WilliTourt/STM32-Desktop-Drumkit/Hardware/Schematic & PCB/Images/MotherBoard_PCB_Bottom.png

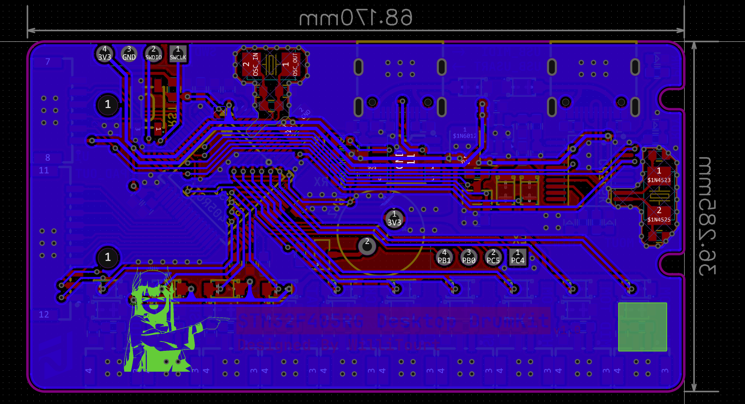
Hardware/Schematic & PCB/Images/MotherBoard_PCB_Bottom.png
