WilliTourt/STM32-Desktop-Drumkit/Hardware/Schematic & PCB/Images/UI_PCB_Top.png

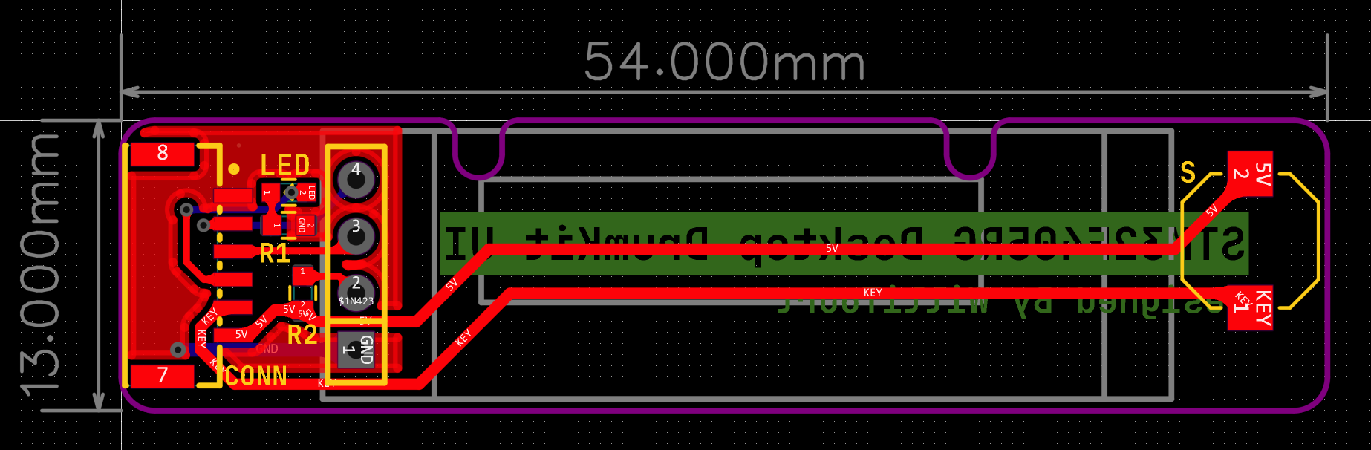
Hardware/Schematic & PCB/Images/UI_PCB_Top.png
