WilliTourt/STM32-Desktop-Drumkit/Images/IMG_20251013_194556.jpg

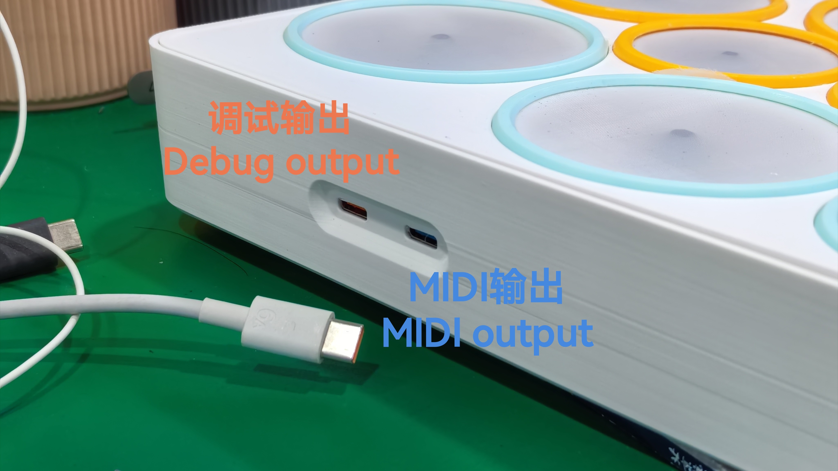
Images/IMG_20251013_194556.jpg
