WilliTourt/STM32-Desktop-Drumkit/Images/IMG_20251013_195028.jpg

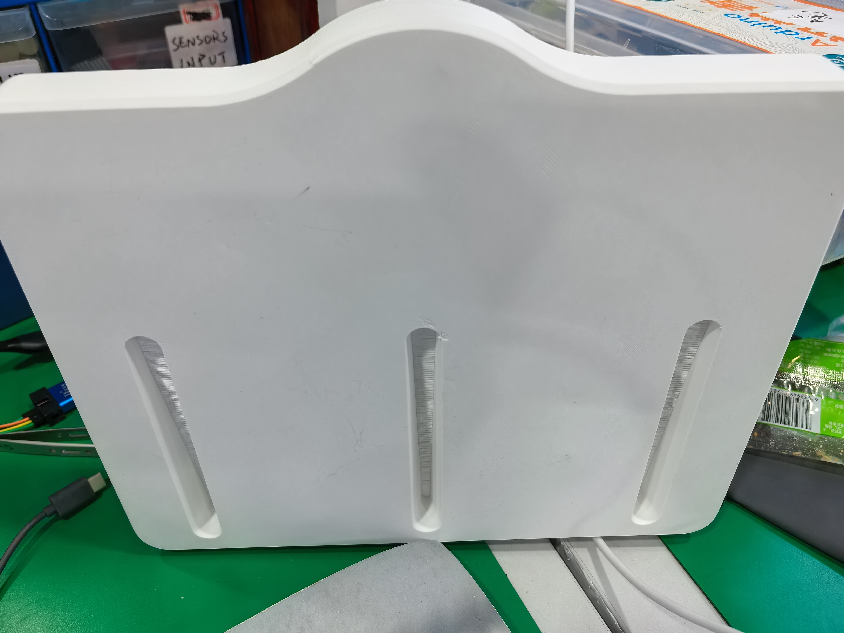
Images/IMG_20251013_195028.jpg
