WilliTourt/STM32-Desktop-Drumkit/Hardware/3D Files/SolidWorks/Tests/DrumpadTestAssemble.SLDASM

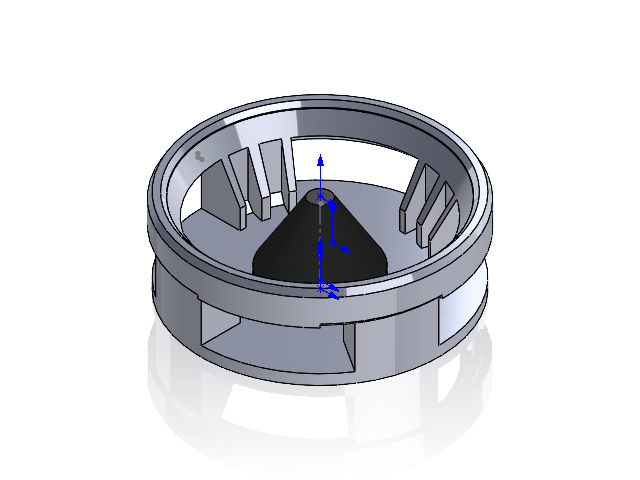
[picture p29: CAD file, 2025-10-13]
Hardware/3D Files/SolidWorks/Tests/DrumpadTestAssemble.SLDASM
DrumpadTest_2
DrumpadTest_Fastener_2
PiezoCone
