WilliTourt/STM32-Desktop-Drumkit/Images/Debug/midi.png

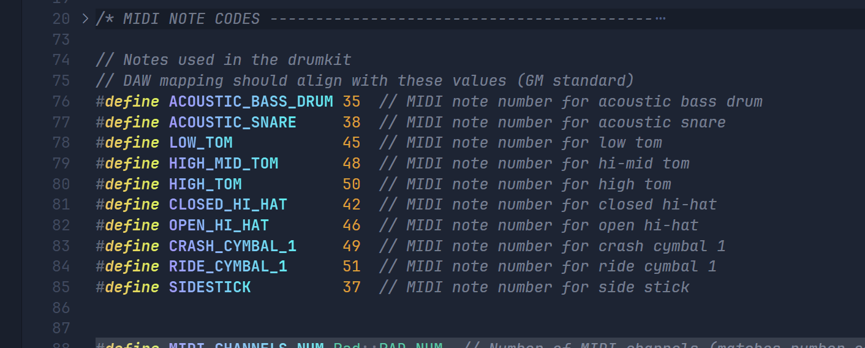
Images/Debug/midi.png
