WilliTourt/STM32-Desktop-Drumkit/Project folder/STM32_Desktop_Drumkit_V1/Components/Inc/config.h

#pragma once

/**
 * @file config.h
 * @brief Centralized configuration for STM32 Desktop Drumkit
 * 
 * This file contains all configurable parameters for the drumkit system.
 * Modify these values to adjust system behavior without changing source code.
 * 
 * @author WilliTourt, willitourt@foxmail.com
 * @copyright Copyright (c) 2025 by WilliTourt
 * 
 */

// =============================================
// Pad Hit Threshold Settings
// =============================================

/**
 * @brief Global offset applied to all pad hit thresholds
 * @note Value range: 0-4095 (12-bit ADC range)
 */
#define _CFG_HIT_THRESHOLD_OFFSET 140

/**
 * @brief Individual pad hit thresholds (ADC values)
 * @note Values should be above noise level but below max playing force
 * @note Typical range: 300-2000 (12-bit ADC)
 */
#define _CFG_OPHIHAT_HIT_THRESHOLD 960 +20  // Open Hi-Hat
#define _CFG_CLHIHAT_HIT_THRESHOLD 732 +20  // Closed Hi-Hat 
#define _CFG_CRASH_HIT_THRESHOLD   631 +20  // Crash Cymbal
#define _CFG_RIDE_HIT_THRESHOLD	   604 +20  // Ride Cymbal
#define _CFG_SSTK_HIT_THRESHOLD    1410+20  // Side Stick
#define _CFG_KICK_HIT_THRESHOLD	   1520+20 // Kick Drum
#define _CFG_SNARE_HIT_THRESHOLD   1488+20  // Snare Drum
#define _CFG_MIDTOM_HIT_THRESHOLD  1024+20  // Mid Tom
#define _CFG_LOWTOM_HIT_THRESHOLD  1161+20  // Low Tom
#define _CFG_HIGHTOM_HIT_THRESHOLD 1288+20  // High Tom

// =============================================
// Pad Upper Limit Settings
// =============================================

/**
 * @brief Maximum force values for each pad (ADC values)
 * @note Used for velocity/force mapping to MIDI (0-127)
 * @note Should be set to typical maximum playing force
 */
#define _CFG_OPHIHAT_MAXF 1579  // Open Hi-Hat
#define _CFG_CLHIHAT_MAXF 1491  // Closed Hi-Hat
#define _CFG_CRASH_H_MAXF 2095  // Crash Cymbal
#define _CFG_RIDE_MAXF    1078  // Ride Cymbal
#define _CFG_SSTK_MAXF    4095  // Side Stick
#define _CFG_KICK_MAXF    1960  // Kick Drum
#define _CFG_SNARE_MAXF   1847  // Snare Drum
#define _CFG_MIDTOM_MAXF  3005  // Mid Tom
#define _CFG_LOWTOM_MAXF  2249  // Low Tom
#define _CFG_HIGHTOM_MAXF 2421  // High Tom

// =============================================
// Force Mapping Curve Settings
// =============================================

/**
 * @brief Force mapping curve types for each pad
 * @note 0: Linear (direct mapping)
 * @note 1: Logarithmic (softer response)
 * @note 2: Exponential (stronger response)
 */
#define _CFG_OPHIHAT_FORCE_CURVE_TYPE 2  // Open Hi-Hat
#define _CFG_CLHIHAT_FORCE_CURVE_TYPE 2  // Closed Hi-Hat
#define _CFG_CRASH_FORCE_CURVE_TYPE   0  // Crash Cymbal
#define _CFG_RIDE_FORCE_CURVE_TYPE    2  // Ride Cymbal
#define _CFG_SSTK_FORCE_CURVE_TYPE    2  // Side Stick
#define _CFG_KICK_FORCE_CURVE_TYPE    2  // Kick Drum
#define _CFG_SNARE_FORCE_CURVE_TYPE   2  // Snare Drum
#define _CFG_MIDTOM_FORCE_CURVE_TYPE  2  // Mid Tom
#define _CFG_LOWTOM_FORCE_CURVE_TYPE  2  // Low Tom
#define _CFG_HIGHTOM_FORCE_CURVE_TYPE 2  // High Tom

// =============================================
// General Pad Settings
// =============================================

/**
 * @brief Time window for force measurement in milliseconds
 * @note Longer windows capture more of the hit but increase latency
 */
#define _CFG_PAD_MEASURING_WINDOW_MS 18

/**
 * @brief When true, set the velocity to _CFG_LOW_VELOCITY_THRESHOLD 
 *        if uint8_t Pad::_force_map(uint16_t adc_val) tend to return
 *        a value below _CFG_LOW_VELOCITY_THRESHOLD.
 */
#define _CFG_FORBID_LOW_VELOCITY true

#define _CFG_LOW_VELOCITY_THRESHOLD 58

// =============================================
// Button Settings
// =============================================

/**
 * @brief Button debounce time in milliseconds
 * @note Prevents false triggers from contact bounce
 */
#define _CFG_BUTTON_DEBOUNCE_TIME_MS       12

/**
 * @brief Maximum time between clicks for single click detection (ms)
 */
#define _CFG_BUTTON_SINGLECLICK_MAXTIME_MS 400

/**
 * @brief Minimum press duration for long press detection (ms)
 */
#define _CFG_BUTTON_LONGPRESS_MINTIME_MS   600

/**
 * @brief Maximum time between clicks for multi-click detection (ms)
 */
#define _CFG_BUTTON_MULTICLICK_MAXTIME_MS  900

// =============================================
// General MIDI Settings
// =============================================

/**
 * @brief MIDI note off signal delay in milliseconds
 */
#define _CFG_NOTEOFF_DELAY_MS     20    

/**
 * @brief MIDI channel ID for drumkit output
 * @note 10 is percussion channel
 */
#define _CFG_MIDI_CHANNEL_ID      10

/**
 * @brief MIDI send timeout in milliseconds
 * @note If a MIDI message is not acknowledged within this time,
 *       it is skiped and midi status will become "Disconnected"
 */
#define _CFG_MIDI_SEND_TIMEOUT_MS 100 

// =============================================
// Other Settings
// =============================================

#define _CFG_BUZZER_DEFAULT_FREQ 1000  // Default buzzer frequency (Hz)
