WilliTourt/STM32-Desktop-Drumkit/Project folder/STM32_Desktop_Drumkit_V1/Components/Inc/oled.h

/**
 * @file oled.h
 * @brief OLED display driver library for STM32 MCUs
 * 
 * Provides control functions for I2C-based OLED displays, supporting:
 * - Text display
 * - Graphics drawing (Dots)
 * - Variable display
 * - Screen control
 * 
 * @author WilliTourt, willitourt@foxmail.com
 * @copyright Copyright (c) 2025 by WilliTourt
 * 
 * @note Comments are mostly written by AI
 */

#pragma once

#include "i2c.h"
#include <stdint.h>
#include <string.h>
#include <stdlib.h>
#include <stdio.h>

/**
 * @brief OLED display I2C device address (7-bit format)
 */
#define OLED_ADDR 0x78

/**
 * @class OLED
 * @brief OLED display control class
 * 
 * Provides basic control functions for OLED displays including:
 * - Text display
 * - Graphics drawing (Dots)
 * - Variable display
 * - Screen control
 */
class OLED {
    public:
        /**
         * @brief Constructor
         * @param hi2c Pointer to I2C handle
         * @param height OLED display height in pixel rows
         */
        OLED(I2C_HandleTypeDef* hi2c, uint8_t height);
        
        /**
         * @brief Initialize OLED display
         * @return true if initialization succeeded
         */
        bool begin();
        
        /**
         * @brief Clear entire display
         */
        void clear();
        
        /**
         * @brief Clear specified display area
         * @param x1 Start column (0-127)
         * @param page1 Start page (0-7)
         * @param x2 End column (0-127)
         * @param page2 End page (0-7)
         */
        void clearPart(uint8_t x1, uint8_t page1, uint8_t x2, uint8_t page2);
        
        /**
         * @brief Set display position
         * @param x Column position (0-127)
         * @param y Row position (0-height-1)
         */
        void setCursor(uint8_t x, uint8_t y);
        
        /**
         * @brief Update display buffer to OLED
         */
        void updateBufferArea();

        /**
         * @brief Set single pixel state
         * @param x Column position (0-127)
         * @param y Row position (0-height-1)
         * @param state Pixel state (true: on, false: off)
         */
        void setPixel(uint8_t x, uint8_t y, bool state);
        
        /**
         * @brief Display text string
         * @param x Start column (0-127)
         * @param y Start row (0-3/7)
         * @param str String to display
         * @param size Font size (1:6x8, 2:8x16)
         */
        void printText(uint8_t x, uint8_t y, const char* str, uint8_t size);
        
        /**
         * @brief Display image
         * @param x Start column (0-127)
         * @param y Start row (0-3/7)
         * @param width Image width
         * @param height Image height
         * @param image Pointer to image data
         */
        void printImage(uint8_t x, uint8_t y, uint8_t width, uint8_t height, const uint8_t* image);
        
        /**
         * @brief Display variable value
         * @param x Start column (0-127)
         * @param y Start row (0-3/7)
         * @param num Number to display
         * @param type Display type ("int","float","hex" etc.)
         * @param length Display length
         * @param zeroPad Whether to zero-pad
         */
        void printVar(uint8_t x, uint8_t y, float num, const char* type, uint8_t length, bool zeroPad);
        
        /**
         * @brief Draw horizontal line
         * @param x Start column (0-127)
         * @param y Row position (0-3/7)
         * @param width Line length
         */
        void printHLine(uint8_t x, uint8_t y, uint8_t width);
        // void printVLine(uint8_t x, uint8_t y, uint8_t height);

        /**
         * @brief Set low brightness mode
         * @param enable Whether to enable low brightness
         */
        void lowBrightness(bool enable);
        
        /**
         * @brief Control OLED power
         * @param state true: power on, false: power off
         */
        void power(bool state);

        const uint8_t ST[160] {
0x00, 0x00, 0x00, 0x00, 0x00, 0x00, 0x00, 0x00, 0xe0, 0xf8, 0xf8, 0xf8, 0xf8, 0xf8, 0xf8, 0xf8, 0xf8, 0xf8, 0xf8, 0xf8, 0xf8, 0xf8, 0xf8, 0xf8, 
0xf8, 0xf8, 0xf8, 0xf8, 0xf8, 0xf8, 0xf8, 0xf8, 0xf8, 0xf8, 0xf8, 0xf8, 0xf8, 0xf8, 0x18, 0x00, 0x00, 0x00, 0x00, 0x00, 0x00, 0xe0, 0xf8, 0xff, 
0xff, 0x07, 0x03, 0x01, 0x70, 0xf8, 0xf8, 0xf8, 0xf8, 0xf8, 0xf8, 0xf8, 0xf8, 0xf8, 0xf8, 0xf8, 0x78, 0x18, 0x00, 0x80, 0xf0, 0xf8, 0xf8, 0xf8, 
0xf8, 0xf8, 0x78, 0x18, 0x00, 0x00, 0x00, 0x00, 0x00, 0x00, 0xc0, 0xf8, 0xff, 0xff, 0xff, 0xff, 0xff, 0xff, 0xfe, 0xfc, 0xf8, 0xf0, 0xe1, 0xc3, 
0x07, 0x0f, 0x1f, 0xff, 0xff, 0xff, 0x1f, 0x03, 0x80, 0xf0, 0xfe, 0xff, 0xff, 0xff, 0xff, 0x7f, 0x0f, 0x03, 0x00, 0x00, 0x00, 0x00, 0x00, 0x00, 
0x00, 0x02, 0x03, 0x03, 0x03, 0x03, 0x03, 0x03, 0x03, 0x03, 0x03, 0x03, 0x03, 0x01, 0x11, 0x10, 0x18, 0x1c, 0x1f, 0x1f, 0x07, 0x00, 0x00, 0x1c, 
0x1f, 0x1f, 0x1f, 0x1f, 0x1f, 0x0f, 0x01, 0x00, 0x00, 0x00, 0x00, 0x00, 0x00, 0x00, 0x00, 0x00, 
};
    private:
        /**
         * @brief Send command to OLED
         * @param command Command byte
         * @return true if command sent successfully
         */
        bool _wCmd(uint8_t command);
        
        /**
         * @brief Send data to OLED
         * @param data Data byte
         */
        void _wData(uint8_t data);
        
        /**
         * @brief Compare two strings
         * @param str1 First string
         * @param str2 Second string
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
            {0x00,0xF0,0xF0,0x10,0x10,0x10,0x10,0x00,0x00,0x1F,0x1F,0x01,0x01,0x01,0x01,0x00},/*"F",38*/
            {0x00,0xE0,0x20,0x10,0x10,0x10,0x10,0x00,0x01,0x0F,0x18,0x10,0x11,0x11,0x1F,0x00},/*"G",39*/
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

        };
};
