WilliTourt/STM32-Desktop-Drumkit/Project folder/STM32_Desktop_Drumkit_V1/Core/Src/adc.c

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
/* Includes ------------------------------------------------------------------*/
#include "adc.h"

ADC_HandleTypeDef hadc1;
ADC_HandleTypeDef hadc2;
ADC_HandleTypeDef hadc3;
DMA_HandleTypeDef hdma_adc1;
DMA_HandleTypeDef hdma_adc2;
DMA_HandleTypeDef hdma_adc3;

/* ADC1 init function */
void MX_ADC1_Init(void)
{

  ADC_ChannelConfTypeDef sConfig = {0};

  /** Configure the global features of the ADC (Clock, Resolution, Data Alignment and number of conversion)
  */
  hadc1.Instance = ADC1;
  hadc1.Init.ClockPrescaler = ADC_CLOCK_SYNC_PCLK_DIV4;
  hadc1.Init.Resolution = ADC_RESOLUTION_12B;
  hadc1.Init.ScanConvMode = ENABLE;
  hadc1.Init.ContinuousConvMode = ENABLE;
  hadc1.Init.DiscontinuousConvMode = DISABLE;
  hadc1.Init.ExternalTrigConvEdge = ADC_EXTERNALTRIGCONVEDGE_NONE;
  hadc1.Init.ExternalTrigConv = ADC_SOFTWARE_START;
  hadc1.Init.DataAlign = ADC_DATAALIGN_RIGHT;
  hadc1.Init.NbrOfConversion = 4;
  hadc1.Init.DMAContinuousRequests = ENABLE;
  hadc1.Init.EOCSelection = ADC_EOC_SINGLE_CONV;
  if (HAL_ADC_Init(&hadc1) != HAL_OK)
  {
    Error_Handler();
  }

  /** Configure for the selected ADC regular channel its corresponding rank in the sequencer and its sample time.
  */
  sConfig.Channel = ADC_CHANNEL_4;
  sConfig.Rank = 1;
  sConfig.SamplingTime = ADC_SAMPLETIME_480CYCLES;
  if (HAL_ADC_ConfigChannel(&hadc1, &sConfig) != HAL_OK)
  {
    Error_Handler();
  }

  /** Configure for the selected ADC regular channel its corresponding rank in the sequencer and its sample time.
  */
  sConfig.Channel = ADC_CHANNEL_5;
  sConfig.Rank = 2;
  if (HAL_ADC_ConfigChannel(&hadc1, &sConfig) != HAL_OK)
  {
    Error_Handler();
  }

  /** Configure for the selected ADC regular channel its corresponding rank in the sequencer and its sample time.
  */
  sConfig.Channel = ADC_CHANNEL_6;
  sConfig.Rank = 3;
  if (HAL_ADC_ConfigChannel(&hadc1, &sConfig) != HAL_OK)
  {
    Error_Handler();
  }

  /** Configure for the selected ADC regular channel its corresponding rank in the sequencer and its sample time.
  */
  sConfig.Channel = ADC_CHANNEL_7;
  sConfig.Rank = 4;
  if (HAL_ADC_ConfigChannel(&hadc1, &sConfig) != HAL_OK)
  {
    Error_Handler();
  }
}
/* ADC2 init function */
void MX_ADC2_Init(void)
{

  ADC_ChannelConfTypeDef sConfig = {0};

  /** Configure the global features of the ADC (Clock, Resolution, Data Alignment and number of conversion)
  */
  hadc2.Instance = ADC2;
  hadc2.Init.ClockPrescaler = ADC_CLOCK_SYNC_PCLK_DIV4;
  hadc2.Init.Resolution = ADC_RESOLUTION_12B;
  hadc2.Init.ScanConvMode = ENABLE;
  hadc2.Init.ContinuousConvMode = ENABLE;
  hadc2.Init.DiscontinuousConvMode = DISABLE;
  hadc2.Init.ExternalTrigConvEdge = ADC_EXTERNALTRIGCONVEDGE_NONE;
  hadc2.Init.ExternalTrigConv = ADC_SOFTWARE_START;
  hadc2.Init.DataAlign = ADC_DATAALIGN_RIGHT;
  hadc2.Init.NbrOfConversion = 3;
  hadc2.Init.DMAContinuousRequests = ENABLE;
  hadc2.Init.EOCSelection = ADC_EOC_SINGLE_CONV;
  if (HAL_ADC_Init(&hadc2) != HAL_OK)
  {
    Error_Handler();
  }

  /** Configure for the selected ADC regular channel its corresponding rank in the sequencer and its sample time.
  */
  sConfig.Channel = ADC_CHANNEL_10;
  sConfig.Rank = 1;
  sConfig.SamplingTime = ADC_SAMPLETIME_480CYCLES;
  if (HAL_ADC_ConfigChannel(&hadc2, &sConfig) != HAL_OK)
  {
    Error_Handler();
  }

  /** Configure for the selected ADC regular channel its corresponding rank in the sequencer and its sample time.
  */
  sConfig.Channel = ADC_CHANNEL_11;
  sConfig.Rank = 2;
  if (HAL_ADC_ConfigChannel(&hadc2, &sConfig) != HAL_OK)
  {
    Error_Handler();
  }

  /** Configure for the selected ADC regular channel its corresponding rank in the sequencer and its sample time.
  */
  sConfig.Channel = ADC_CHANNEL_12;
  sConfig.Rank = 3;
  if (HAL_ADC_ConfigChannel(&hadc2, &sConfig) != HAL_OK)
  {
    Error_Handler();
  }
}
/* ADC3 init function */
void MX_ADC3_Init(void)
{

  ADC_ChannelConfTypeDef sConfig = {0};

  /** Configure the global features of the ADC (Clock, Resolution, Data Alignment and number of conversion)
  */
  hadc3.Instance = ADC3;
  hadc3.Init.ClockPrescaler = ADC_CLOCK_SYNC_PCLK_DIV4;
  hadc3.Init.Resolution = ADC_RESOLUTION_12B;
  hadc3.Init.ScanConvMode = ENABLE;
  hadc3.Init.ContinuousConvMode = ENABLE;
  hadc3.Init.DiscontinuousConvMode = DISABLE;
  hadc3.Init.ExternalTrigConvEdge = ADC_EXTERNALTRIGCONVEDGE_NONE;
  hadc3.Init.ExternalTrigConv = ADC_SOFTWARE_START;
  hadc3.Init.DataAlign = ADC_DATAALIGN_RIGHT;
  hadc3.Init.NbrOfConversion = 3;
  hadc3.Init.DMAContinuousRequests = ENABLE;
  hadc3.Init.EOCSelection = ADC_EOC_SINGLE_CONV;
  if (HAL_ADC_Init(&hadc3) != HAL_OK)
  {
    Error_Handler();
  }

  /** Configure for the selected ADC regular channel its corresponding rank in the sequencer and its sample time.
  */
  sConfig.Channel = ADC_CHANNEL_0;
  sConfig.Rank = 1;
  sConfig.SamplingTime = ADC_SAMPLETIME_480CYCLES;
  if (HAL_ADC_ConfigChannel(&hadc3, &sConfig) != HAL_OK)
  {
    Error_Handler();
  }

  /** Configure for the selected ADC regular channel its corresponding rank in the sequencer and its sample time.
  */
  sConfig.Channel = ADC_CHANNEL_1;
  sConfig.Rank = 2;
  if (HAL_ADC_ConfigChannel(&hadc3, &sConfig) != HAL_OK)
  {
    Error_Handler();
  }

  /** Configure for the selected ADC regular channel its corresponding rank in the sequencer and its sample time.
  */
  sConfig.Channel = ADC_CHANNEL_13;
  sConfig.Rank = 3;
  if (HAL_ADC_ConfigChannel(&hadc3, &sConfig) != HAL_OK)
  {
    Error_Handler();
  }
}

void HAL_ADC_MspInit(ADC_HandleTypeDef* adcHandle)
{

  GPIO_InitTypeDef GPIO_InitStruct = {0};
  if(adcHandle->Instance==ADC1)
  {
    /* ADC1 clock enable */
    __HAL_RCC_ADC1_CLK_ENABLE();

    __HAL_RCC_GPIOA_CLK_ENABLE();
    /**ADC1 GPIO Configuration
    PA4     ------> ADC1_IN4
    PA5     ------> ADC1_IN5
    PA6     ------> ADC1_IN6
    PA7     ------> ADC1_IN7
    */
    GPIO_InitStruct.Pin = OPENHIHAT_ADC_Pin|CLOSEHIHAT_ADC_Pin|CRASH_ADC_Pin|RIDE_ADC_Pin;
    GPIO_InitStruct.Mode = GPIO_MODE_ANALOG;
    GPIO_InitStruct.Pull = GPIO_NOPULL;
    HAL_GPIO_Init(GPIOA, &GPIO_InitStruct);

    /* ADC1 DMA Init */
    /* ADC1 Init */
    hdma_adc1.Instance = DMA2_Stream0;
    hdma_adc1.Init.Channel = DMA_CHANNEL_0;
    hdma_adc1.Init.Direction = DMA_PERIPH_TO_MEMORY;
    hdma_adc1.Init.PeriphInc = DMA_PINC_DISABLE;
    hdma_adc1.Init.MemInc = DMA_MINC_ENABLE;
    hdma_adc1.Init.PeriphDataAlignment = DMA_PDATAALIGN_HALFWORD;
    hdma_adc1.Init.MemDataAlignment = DMA_MDATAALIGN_HALFWORD;
    hdma_adc1.Init.Mode = DMA_CIRCULAR;
    hdma_adc1.Init.Priority = DMA_PRIORITY_HIGH;
    hdma_adc1.Init.FIFOMode = DMA_FIFOMODE_DISABLE;
    if (HAL_DMA_Init(&hdma_adc1) != HAL_OK)
    {
      Error_Handler();
    }

    __HAL_LINKDMA(adcHandle,DMA_Handle,hdma_adc1);

    /* ADC1 interrupt Init */
    HAL_NVIC_SetPriority(ADC_IRQn, 0, 0);
    HAL_NVIC_EnableIRQ(ADC_IRQn);
  }
  else if(adcHandle->Instance==ADC2)
  {
    /* ADC2 clock enable */
    __HAL_RCC_ADC2_CLK_ENABLE();

    __HAL_RCC_GPIOC_CLK_ENABLE();
    /**ADC2 GPIO Configuration
    PC0     ------> ADC2_IN10
    PC1     ------> ADC2_IN11
    PC2     ------> ADC2_IN12
    */
    GPIO_InitStruct.Pin = SIDESTICK_ADC_Pin|KICK_ADC_Pin|SNARE_ADC_Pin;
    GPIO_InitStruct.Mode = GPIO_MODE_ANALOG;
    GPIO_InitStruct.Pull = GPIO_NOPULL;
    HAL_GPIO_Init(GPIOC, &GPIO_InitStruct);

    /* ADC2 DMA Init */
    /* ADC2 Init */
    hdma_adc2.Instance = DMA2_Stream2;
    hdma_adc2.Init.Channel = DMA_CHANNEL_1;
    hdma_adc2.Init.Direction = DMA_PERIPH_TO_MEMORY;
    hdma_adc2.Init.PeriphInc = DMA_PINC_DISABLE;
    hdma_adc2.Init.MemInc = DMA_MINC_ENABLE;
    hdma_adc2.Init.PeriphDataAlignment = DMA_PDATAALIGN_HALFWORD;
    hdma_adc2.Init.MemDataAlignment = DMA_MDATAALIGN_HALFWORD;
    hdma_adc2.Init.Mode = DMA_CIRCULAR;
    hdma_adc2.Init.Priority = DMA_PRIORITY_HIGH;
    hdma_adc2.Init.FIFOMode = DMA_FIFOMODE_DISABLE;
    if (HAL_DMA_Init(&hdma_adc2) != HAL_OK)
    {
      Error_Handler();
    }

    __HAL_LINKDMA(adcHandle,DMA_Handle,hdma_adc2);

    /* ADC2 interrupt Init */
    HAL_NVIC_SetPriority(ADC_IRQn, 0, 0);
    HAL_NVIC_EnableIRQ(ADC_IRQn);
  }
  else if(adcHandle->Instance==ADC3)
  {
    /* ADC3 clock enable */
    __HAL_RCC_ADC3_CLK_ENABLE();

    __HAL_RCC_GPIOC_CLK_ENABLE();
    __HAL_RCC_GPIOA_CLK_ENABLE();
    /**ADC3 GPIO Configuration
    PC3     ------> ADC3_IN13
    PA0-WKUP     ------> ADC3_IN0
    PA1     ------> ADC3_IN1
    */
    GPIO_InitStruct.Pin = HT_ADC_Pin;
    GPIO_InitStruct.Mode = GPIO_MODE_ANALOG;
    GPIO_InitStruct.Pull = GPIO_NOPULL;
    HAL_GPIO_Init(HT_ADC_GPIO_Port, &GPIO_InitStruct);

    GPIO_InitStruct.Pin = MT_ADC_Pin|LT_ADC_Pin;
    GPIO_InitStruct.Mode = GPIO_MODE_ANALOG;
    GPIO_InitStruct.Pull = GPIO_NOPULL;
    HAL_GPIO_Init(GPIOA, &GPIO_InitStruct);

    /* ADC3 DMA Init */
    /* ADC3 Init */
    hdma_adc3.Instance = DMA2_Stream1;
    hdma_adc3.Init.Channel = DMA_CHANNEL_2;
    hdma_adc3.Init.Direction = DMA_PERIPH_TO_MEMORY;
    hdma_adc3.Init.PeriphInc = DMA_PINC_DISABLE;
    hdma_adc3.Init.MemInc = DMA_MINC_ENABLE;
    hdma_adc3.Init.PeriphDataAlignment = DMA_PDATAALIGN_HALFWORD;
    hdma_adc3.Init.MemDataAlignment = DMA_MDATAALIGN_HALFWORD;
    hdma_adc3.Init.Mode = DMA_CIRCULAR;
    hdma_adc3.Init.Priority = DMA_PRIORITY_HIGH;
    hdma_adc3.Init.FIFOMode = DMA_FIFOMODE_DISABLE;
    if (HAL_DMA_Init(&hdma_adc3) != HAL_OK)
    {
      Error_Handler();
    }

    __HAL_LINKDMA(adcHandle,DMA_Handle,hdma_adc3);

    /* ADC3 interrupt Init */
    HAL_NVIC_SetPriority(ADC_IRQn, 0, 0);
    HAL_NVIC_EnableIRQ(ADC_IRQn);
  }
}

void HAL_ADC_MspDeInit(ADC_HandleTypeDef* adcHandle)
{

  if(adcHandle->Instance==ADC1)
  {
    /* Peripheral clock disable */
    __HAL_RCC_ADC1_CLK_DISABLE();

    /**ADC1 GPIO Configuration
    PA4     ------> ADC1_IN4
    PA5     ------> ADC1_IN5
    PA6     ------> ADC1_IN6
    PA7     ------> ADC1_IN7
    */
    HAL_GPIO_DeInit(GPIOA, OPENHIHAT_ADC_Pin|CLOSEHIHAT_ADC_Pin|CRASH_ADC_Pin|RIDE_ADC_Pin);

    /* ADC1 DMA DeInit */
    HAL_DMA_DeInit(adcHandle->DMA_Handle);

    /* ADC1 interrupt Deinit */
  /* USER CODE BEGIN ADC1:ADC_IRQn disable */
    /**
    * Uncomment the line below to disable the "ADC_IRQn" interrupt
    * Be aware, disabling shared interrupt may affect other IPs
    */
    /* HAL_NVIC_DisableIRQ(ADC_IRQn); */
  /* USER CODE END ADC1:ADC_IRQn disable */

  }
  else if(adcHandle->Instance==ADC2)
  {
    /* Peripheral clock disable */
    __HAL_RCC_ADC2_CLK_DISABLE();

    /**ADC2 GPIO Configuration
    PC0     ------> ADC2_IN10
    PC1     ------> ADC2_IN11
    PC2     ------> ADC2_IN12
    */
    HAL_GPIO_DeInit(GPIOC, SIDESTICK_ADC_Pin|KICK_ADC_Pin|SNARE_ADC_Pin);

    /* ADC2 DMA DeInit */
    HAL_DMA_DeInit(adcHandle->DMA_Handle);

    /* ADC2 interrupt Deinit */
  /* USER CODE BEGIN ADC2:ADC_IRQn disable */
    /**
    * Uncomment the line below to disable the "ADC_IRQn" interrupt
    * Be aware, disabling shared interrupt may affect other IPs
    */
    /* HAL_NVIC_DisableIRQ(ADC_IRQn); */
  /* USER CODE END ADC2:ADC_IRQn disable */

  }
  else if(adcHandle->Instance==ADC3)
  {
    /* Peripheral clock disable */
    __HAL_RCC_ADC3_CLK_DISABLE();

    /**ADC3 GPIO Configuration
    PC3     ------> ADC3_IN13
    PA0-WKUP     ------> ADC3_IN0
    PA1     ------> ADC3_IN1
    */
    HAL_GPIO_DeInit(HT_ADC_GPIO_Port, HT_ADC_Pin);

    HAL_GPIO_DeInit(GPIOA, MT_ADC_Pin|LT_ADC_Pin);

    /* ADC3 DMA DeInit */
    HAL_DMA_DeInit(adcHandle->DMA_Handle);

    /* ADC3 interrupt Deinit */
  /* USER CODE BEGIN ADC3:ADC_IRQn disable */
    /**
    * Uncomment the line below to disable the "ADC_IRQn" interrupt
    * Be aware, disabling shared interrupt may affect other IPs
    */
    /* HAL_NVIC_DisableIRQ(ADC_IRQn); */
  /* USER CODE END ADC3:ADC_IRQn disable */

  }
}
