WilliTourt/STM32-Desktop-Drumkit/Project folder/STM32_Desktop_Drumkit_V1/Components/Inc/cpp_main.h

#ifndef CPP_MAIN_H_
#define CPP_MAIN_H_

#ifdef __cplusplus
extern "C"
{
#endif

#include "main.h"
#include "usart.h"


#include "config.h" // This file contains all the configuration parameters

int cpp_main();

#ifdef __cplusplus
}
#endif

extern void DBG(const char* str);
extern char dbg_buf[128];

#endif
